tenorangesax/SaxboardTM/Pictures/IMG_7189.jpeg

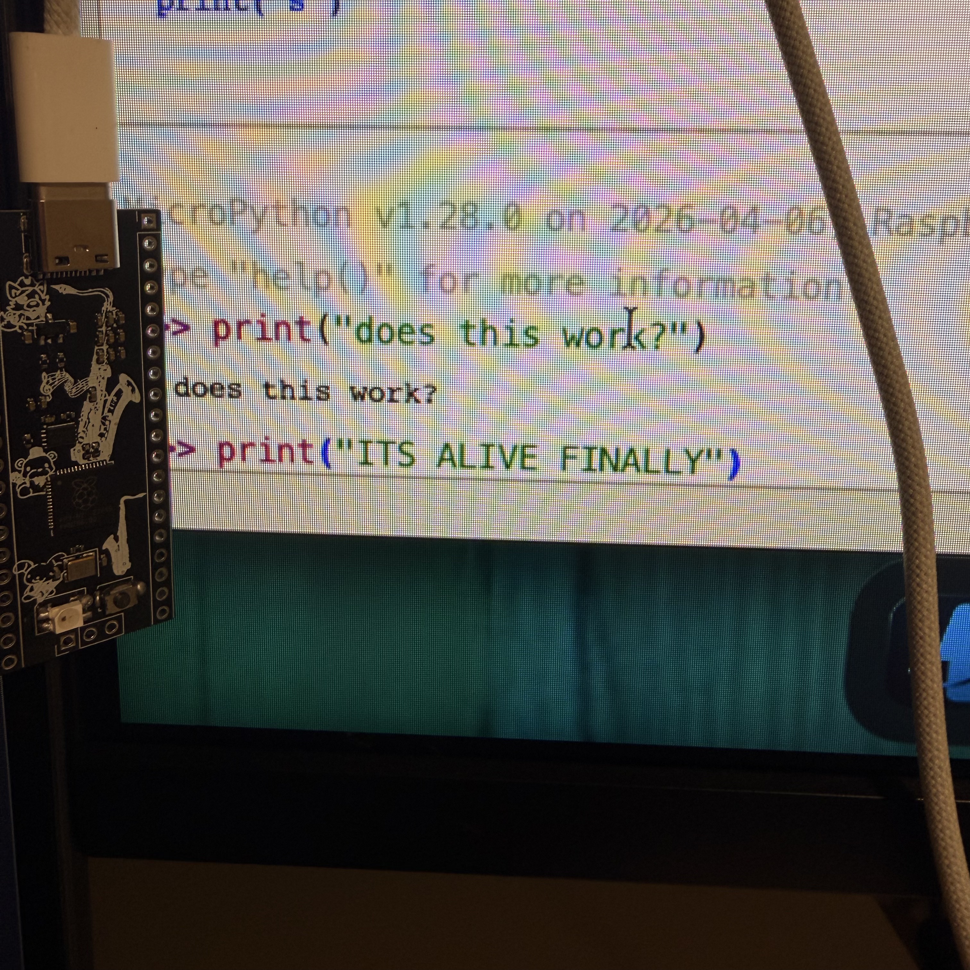
Pictures/IMG_7189.jpeg
