tenorangesax/SaxboardTM/Pictures/IMG_7191.jpeg

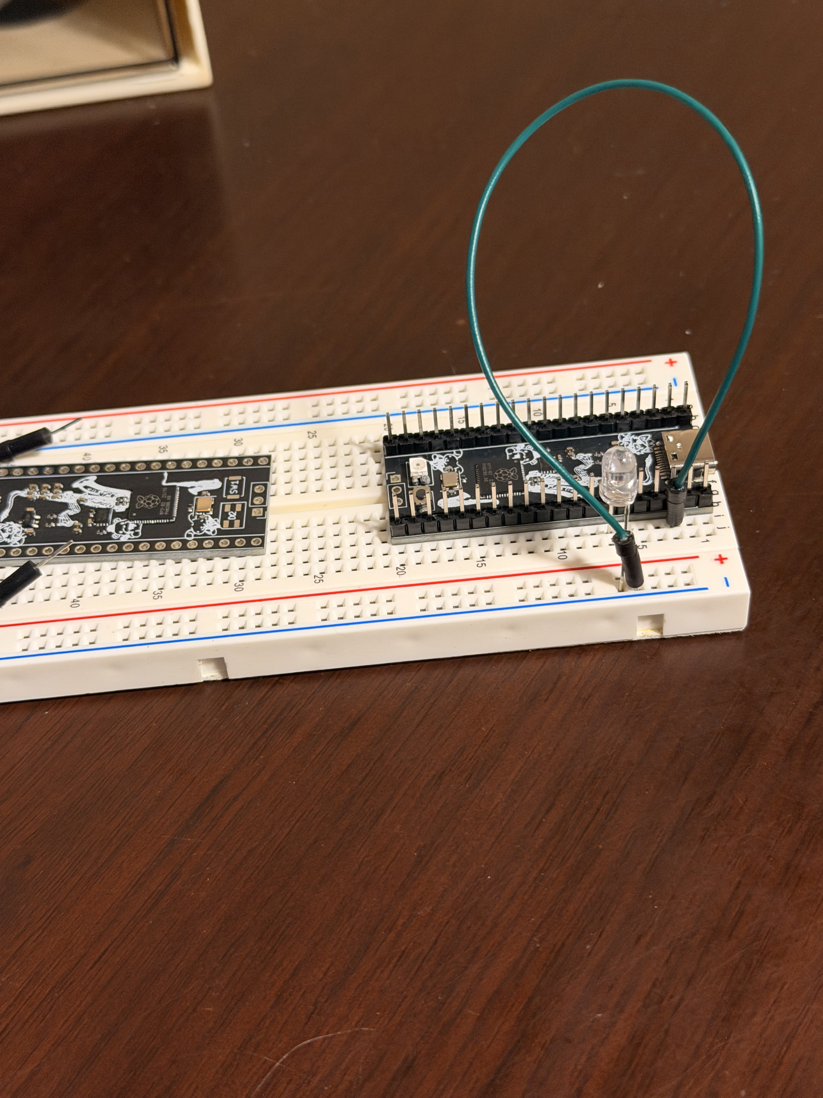
Pictures/IMG_7191.jpeg
