tenorangesax/SaxboardTM/Pictures/1.png

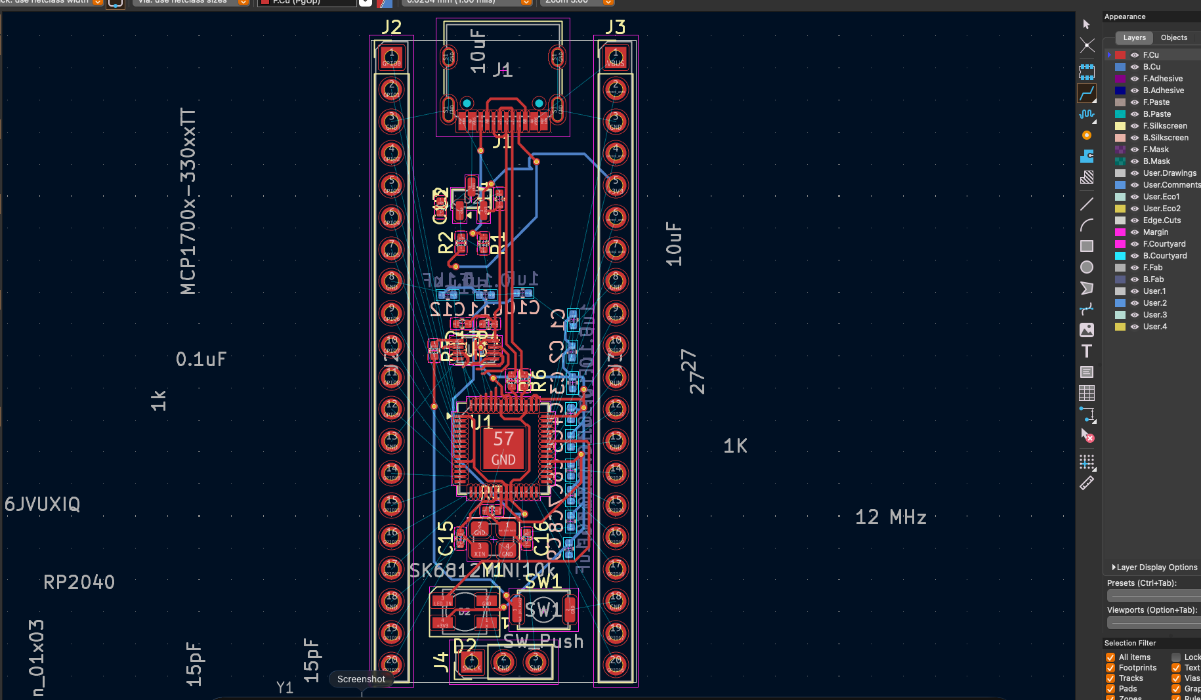
Pictures/1.png
