tenorangesax/SaxboardTM/Pictures/2.png

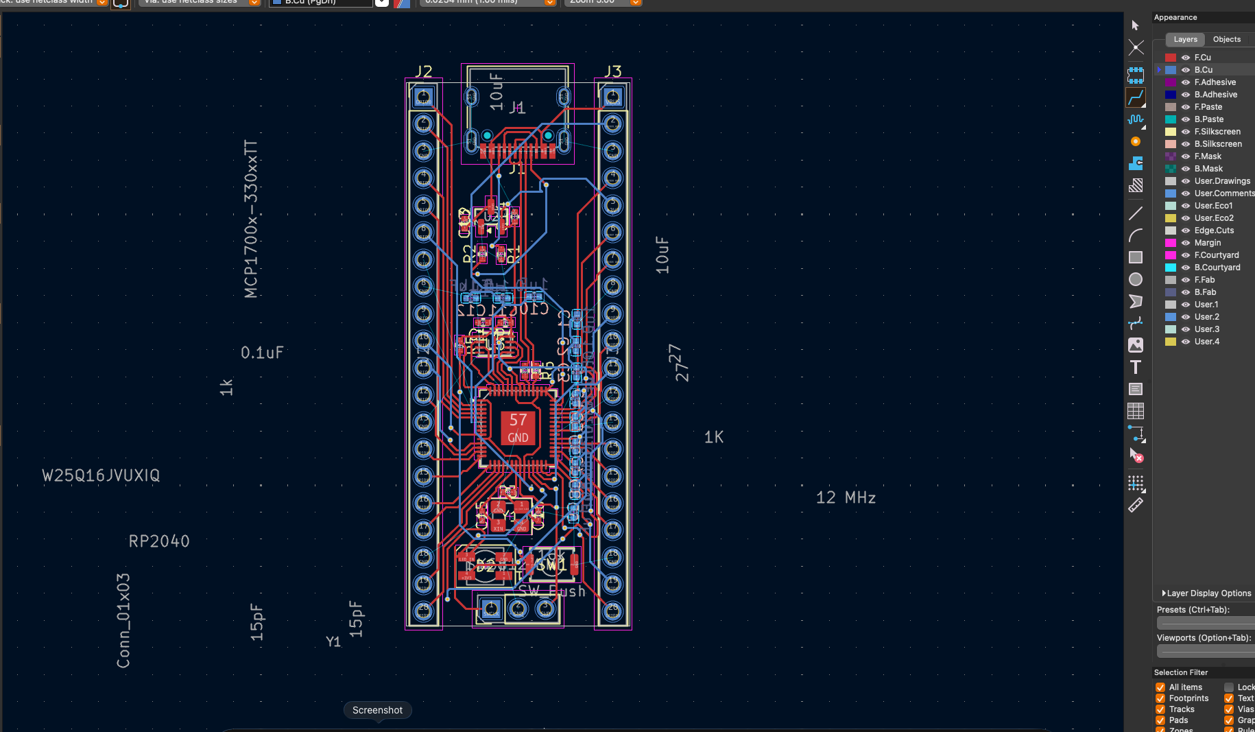
Pictures/2.png
