tenorangesax/SaxboardTM/Pictures/3.png

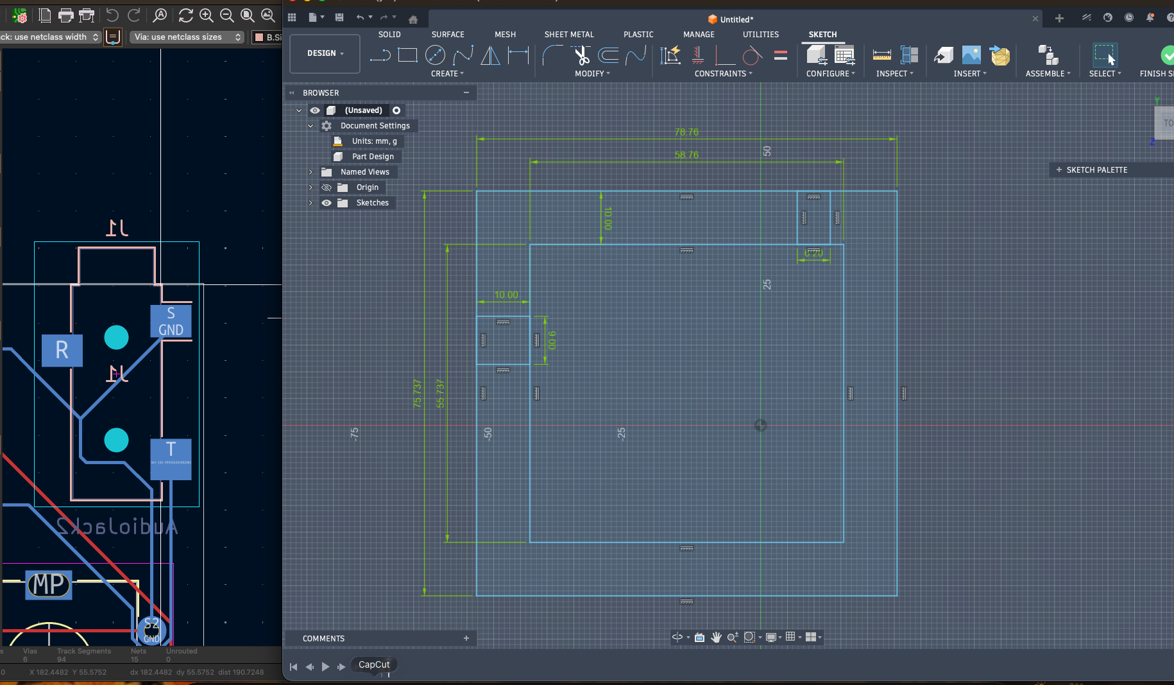
Pictures/3.png
