tenorangesax/SaxboardTM/Pictures/4.png

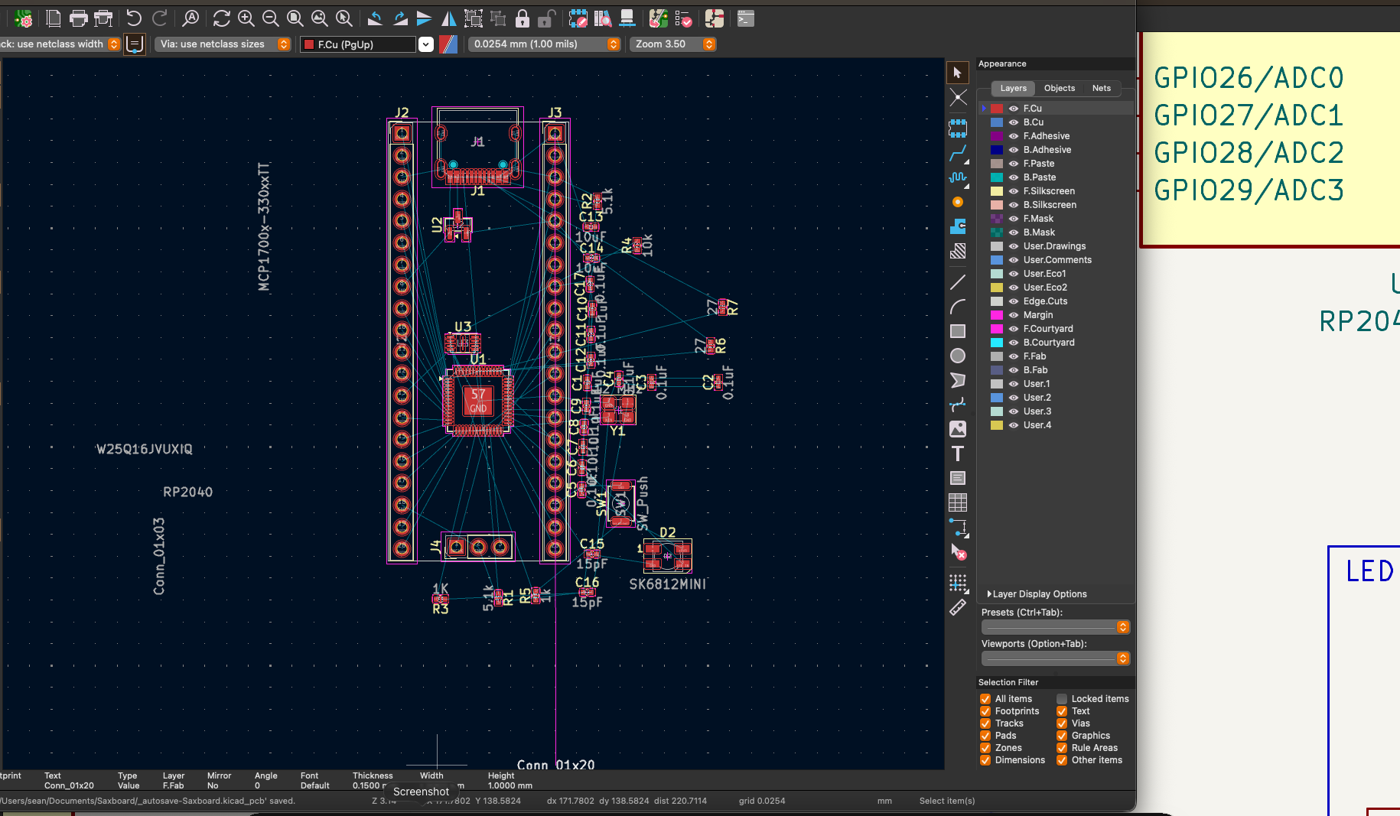
Pictures/4.png
