tenorangesax/SaxboardTM/Pictures/5.png

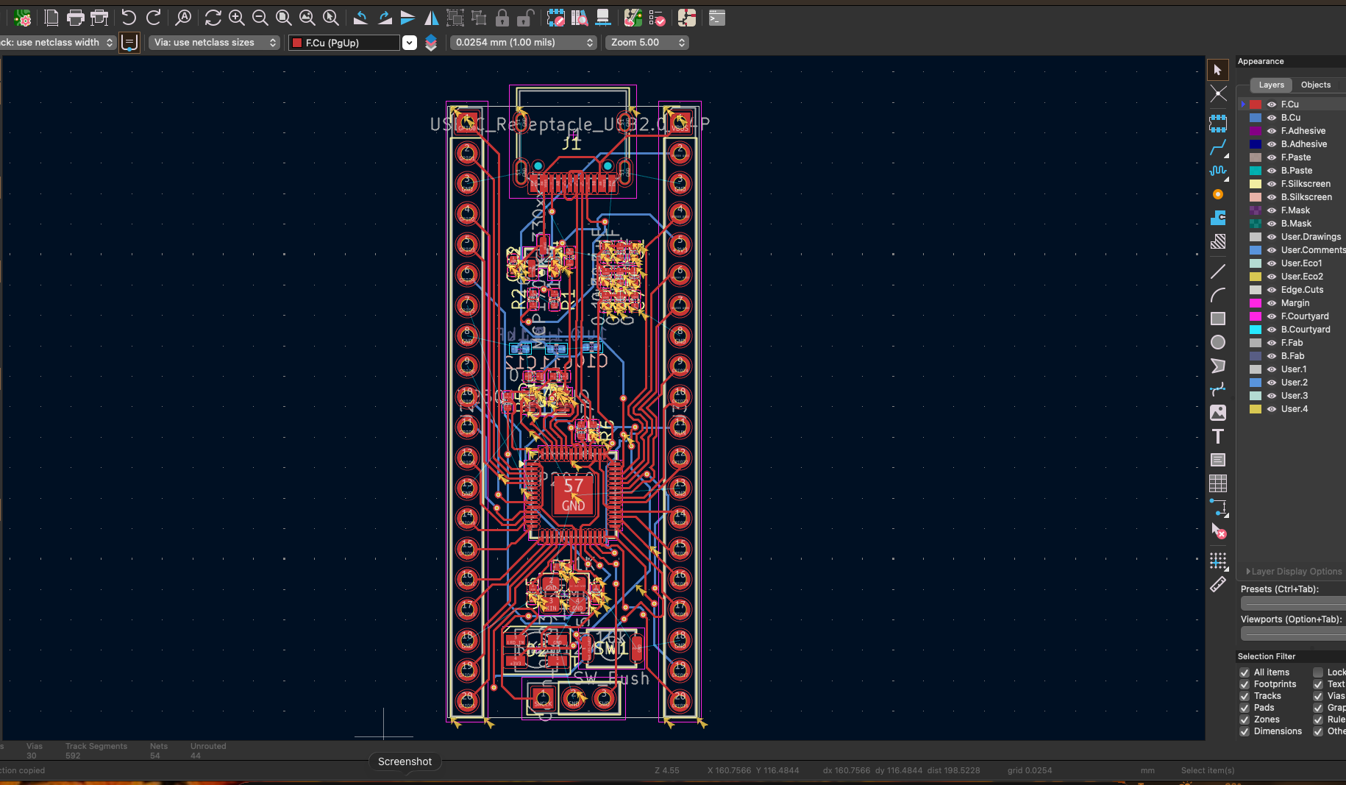
Pictures/5.png
