tenorangesax/SaxboardTM/Pictures/6.png

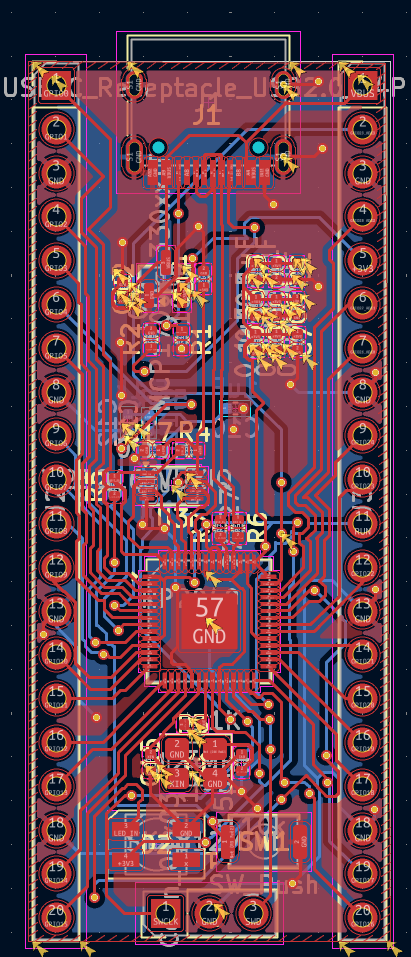
Pictures/6.png
