tenorangesax/SaxboardTM/Pictures/final editor 2.png

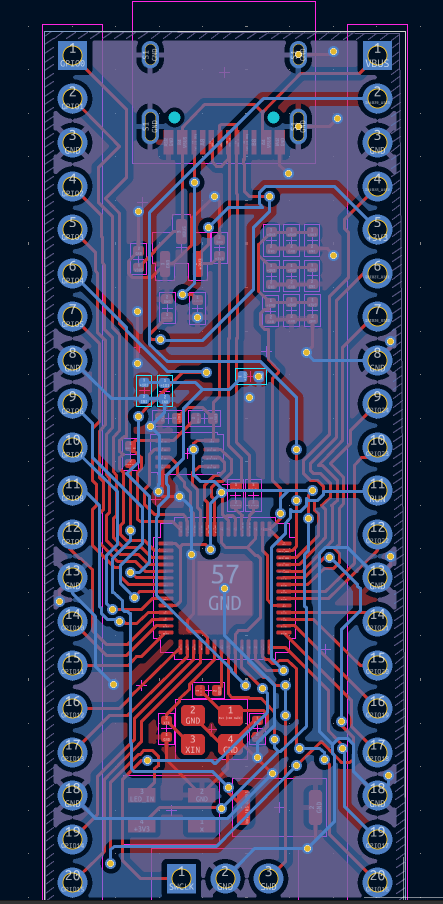
Pictures/final editor 2.png
