tenorangesax/SaxboardTM/Pictures/final editor 3.png

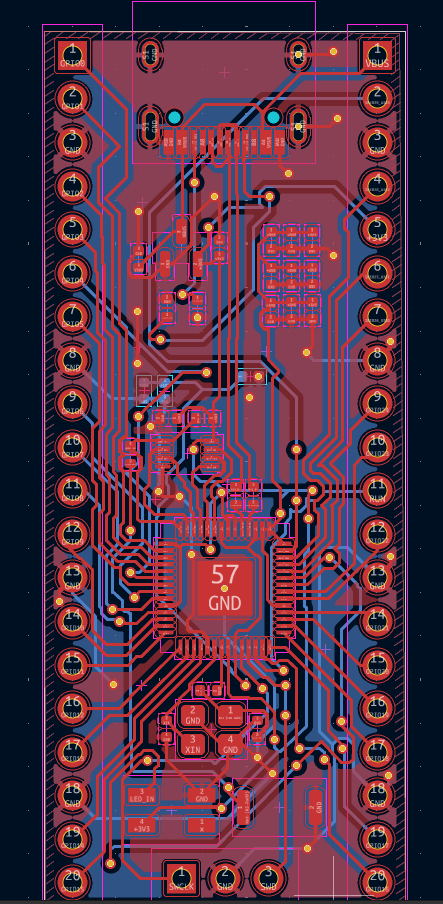
Pictures/final editor 3.png
