tenorangesax/SaxboardTM/Pictures/final editor.png

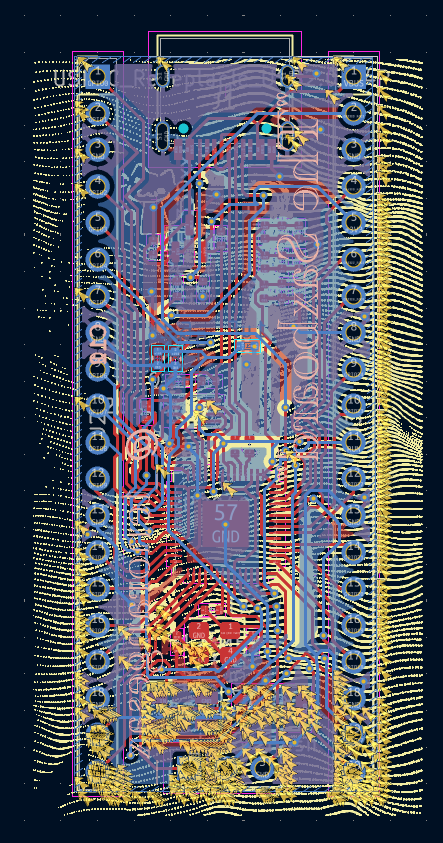
Pictures/final editor.png
