tenorangesax/SaxboardTM/Pictures/Final pcb angle view.png

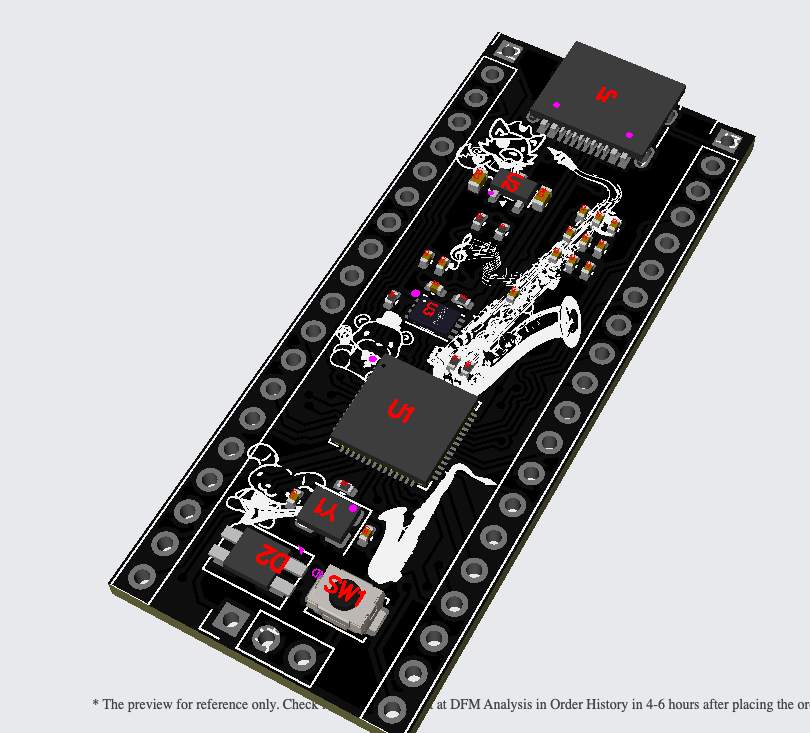
Pictures/Final pcb angle view.png
