tenorangesax/SaxboardTM/Pictures/Final pcb back view.png

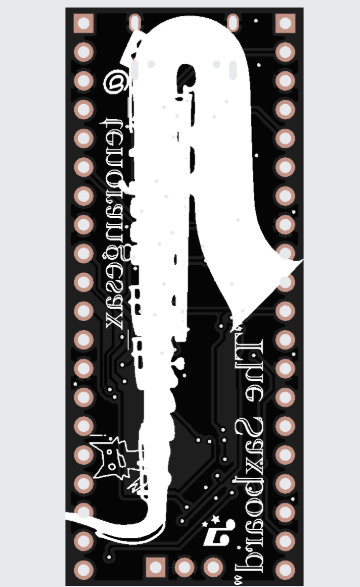
Pictures/Final pcb back view.png
