tenorangesax/SaxboardTM/Pictures/Final pcb front view.png

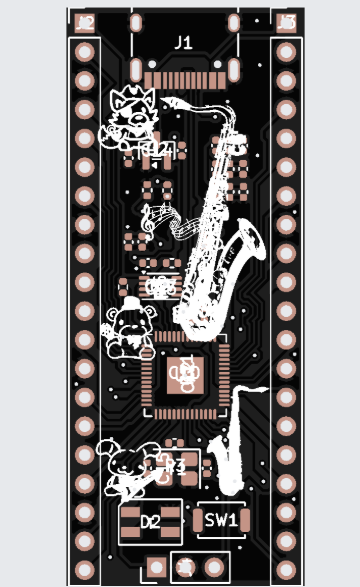
Pictures/Final pcb front view.png
