tenorangesax/SaxboardTM/Pictures/Footprints.png

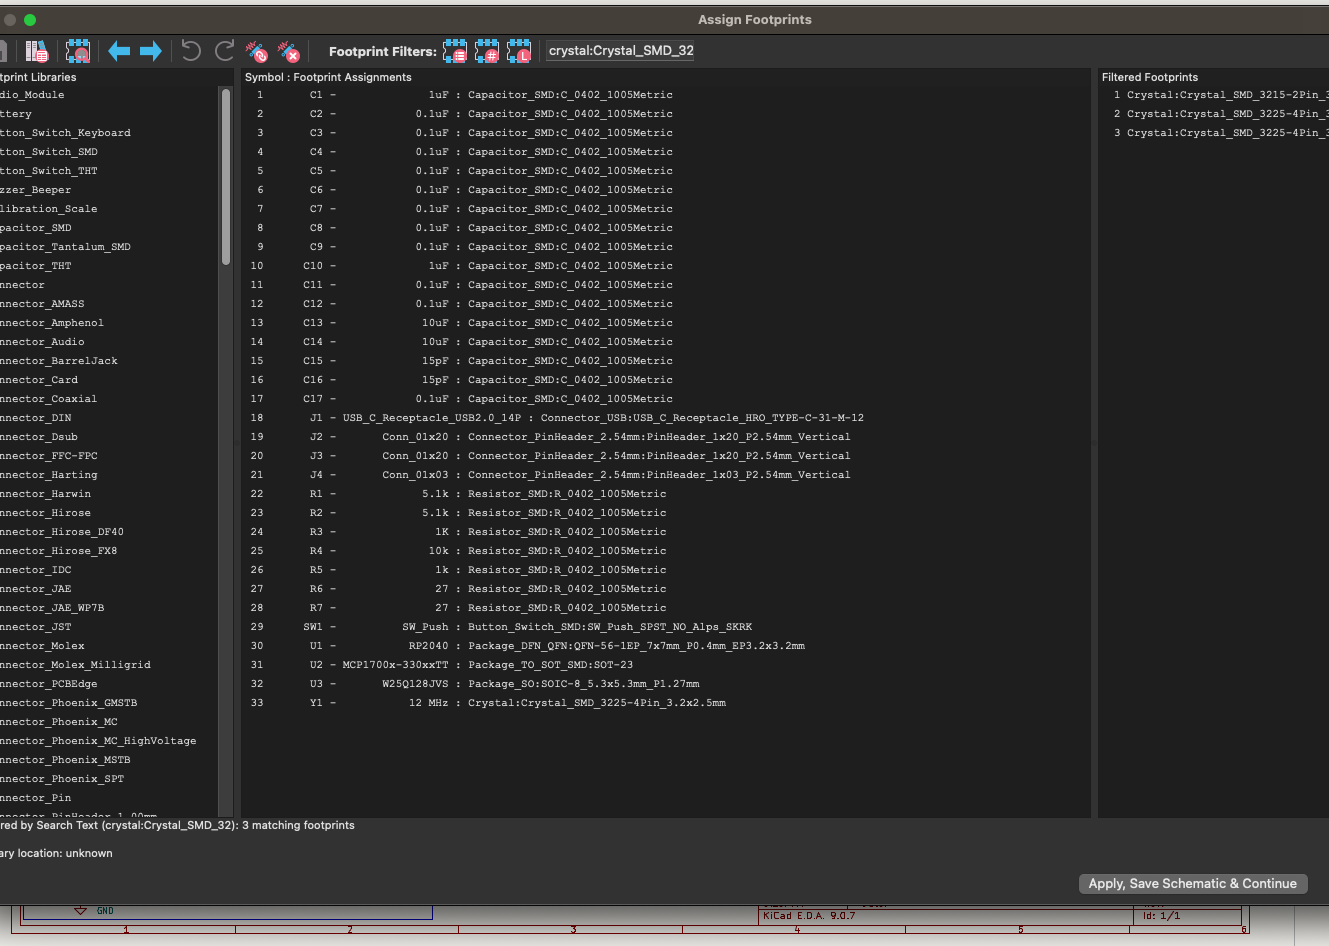
Pictures/Footprints.png
