tenorangesax/SaxboardTM/Pictures/IMG_7158.jpeg

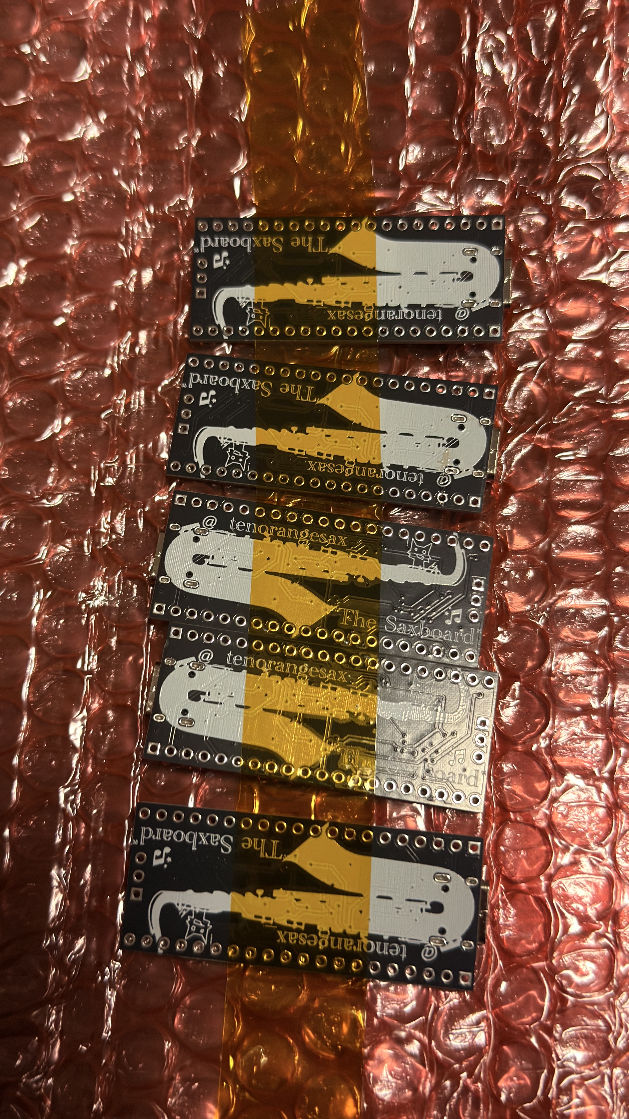
Pictures/IMG_7158.jpeg
