tenorangesax/SaxboardTM/Pictures/IMG_7160.jpeg

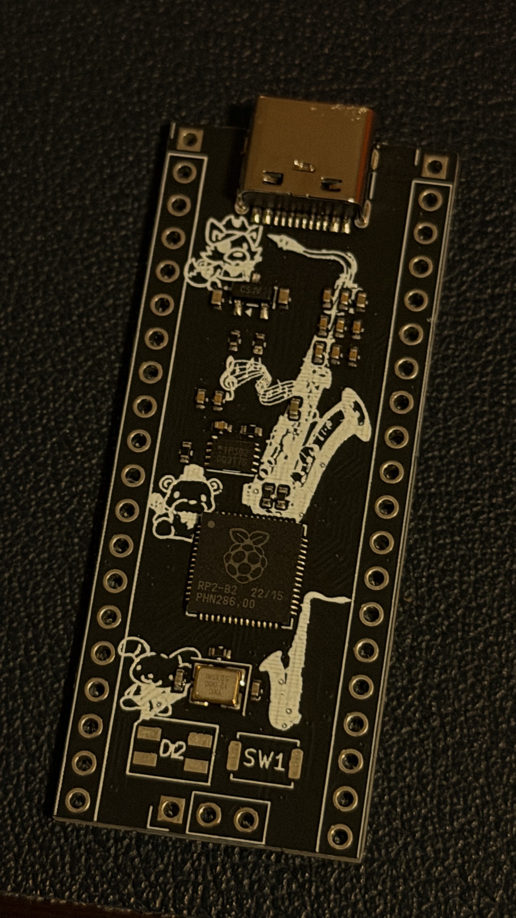
Pictures/IMG_7160.jpeg
