tenorangesax/SaxboardTM/Pictures/IMG_7161.jpeg

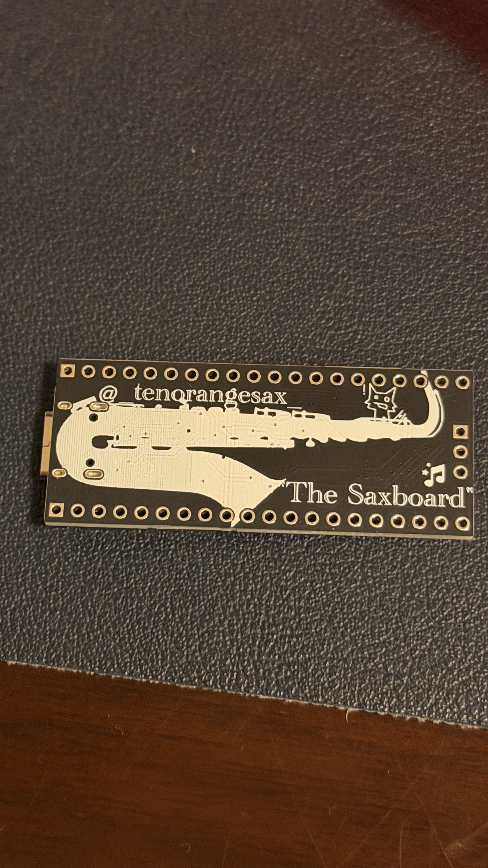
Pictures/IMG_7161.jpeg
