tenorangesax/SaxboardTM/Pictures/IMG_7163.jpeg

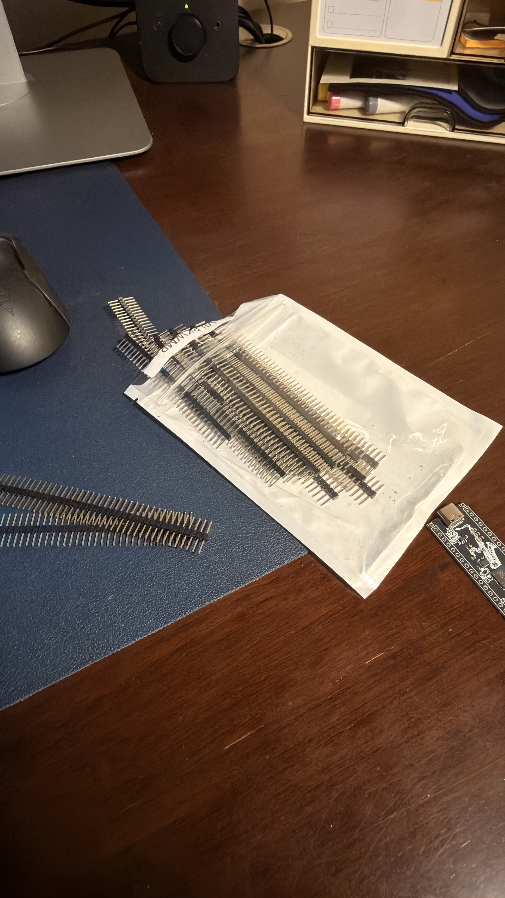
Pictures/IMG_7163.jpeg
