tenorangesax/SaxboardTM/Pictures/IMG_7164.jpeg

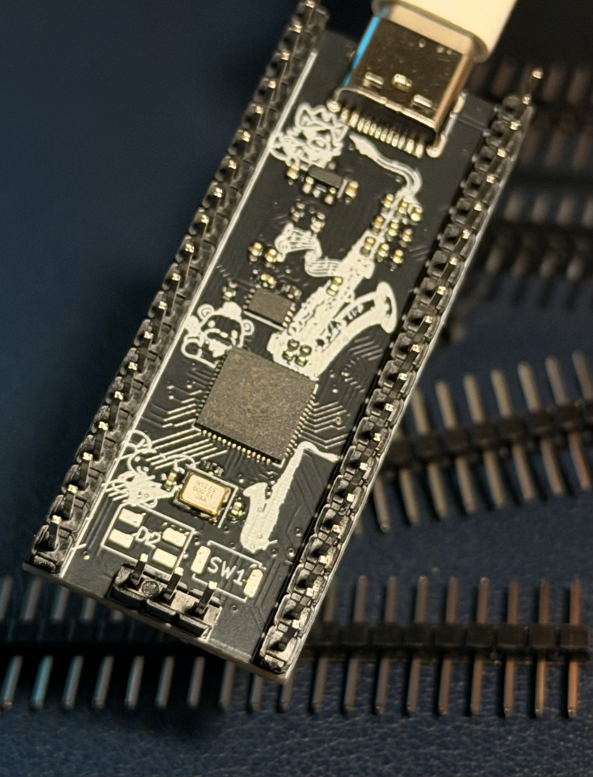
Pictures/IMG_7164.jpeg
