tenorangesax/SaxboardTM/Pictures/IMG_7166.jpeg

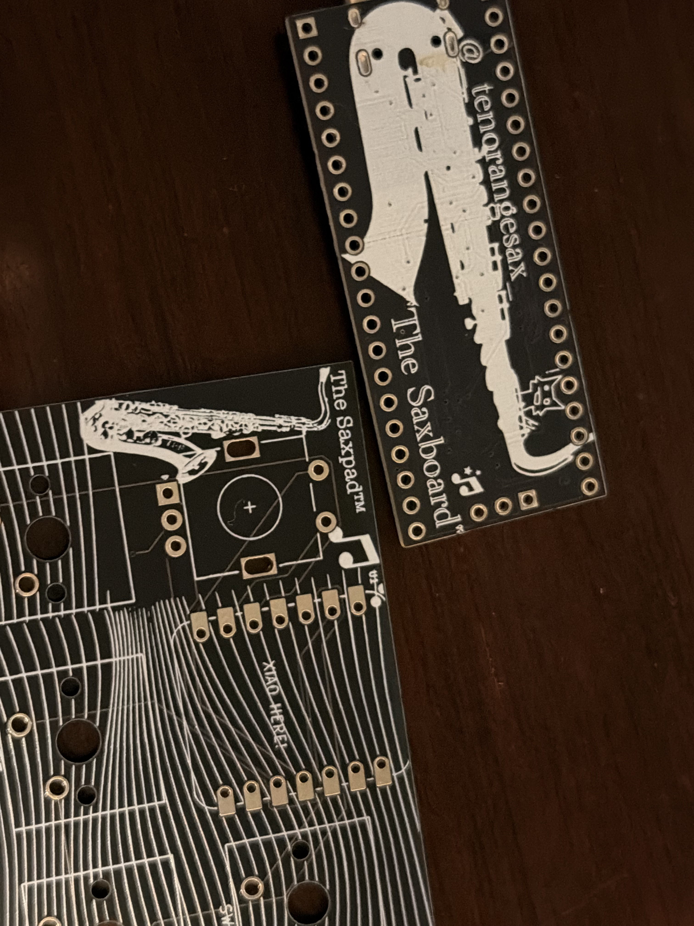
Pictures/IMG_7166.jpeg
