tenorangesax/SaxboardTM/Pictures/IMG_7169.jpeg

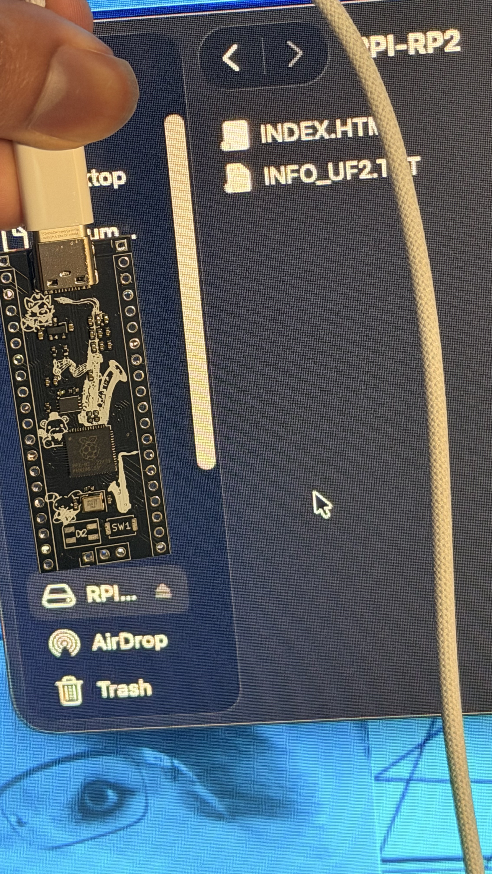
Pictures/IMG_7169.jpeg
