tenorangesax/SaxboardTM/Pictures/IMG_7171.jpeg

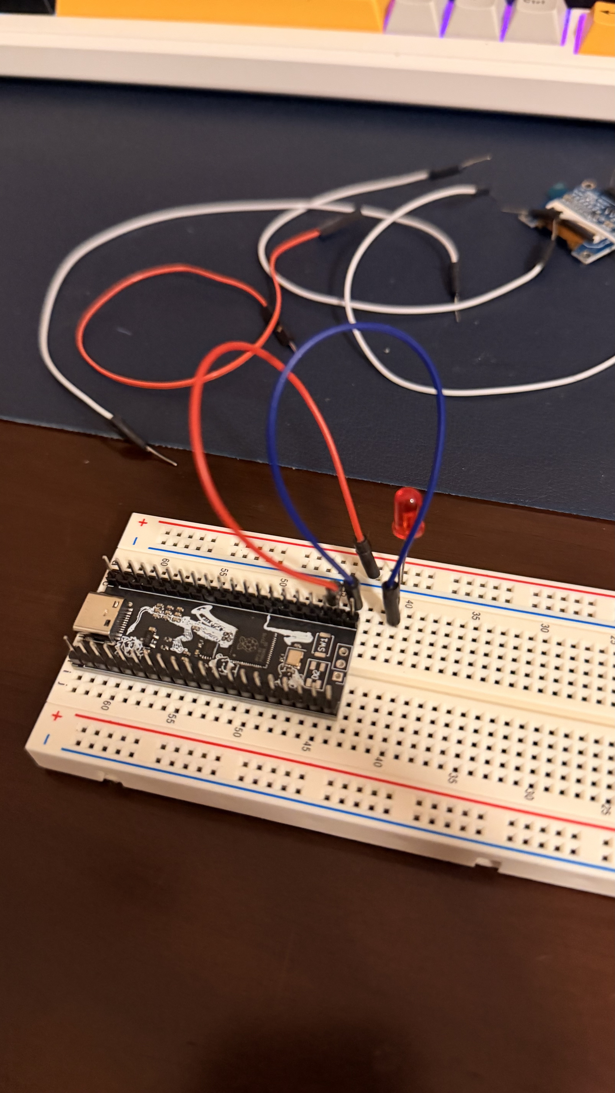
Pictures/IMG_7171.jpeg
