tenorangesax/SaxboardTM/Pictures/Saxboard.png

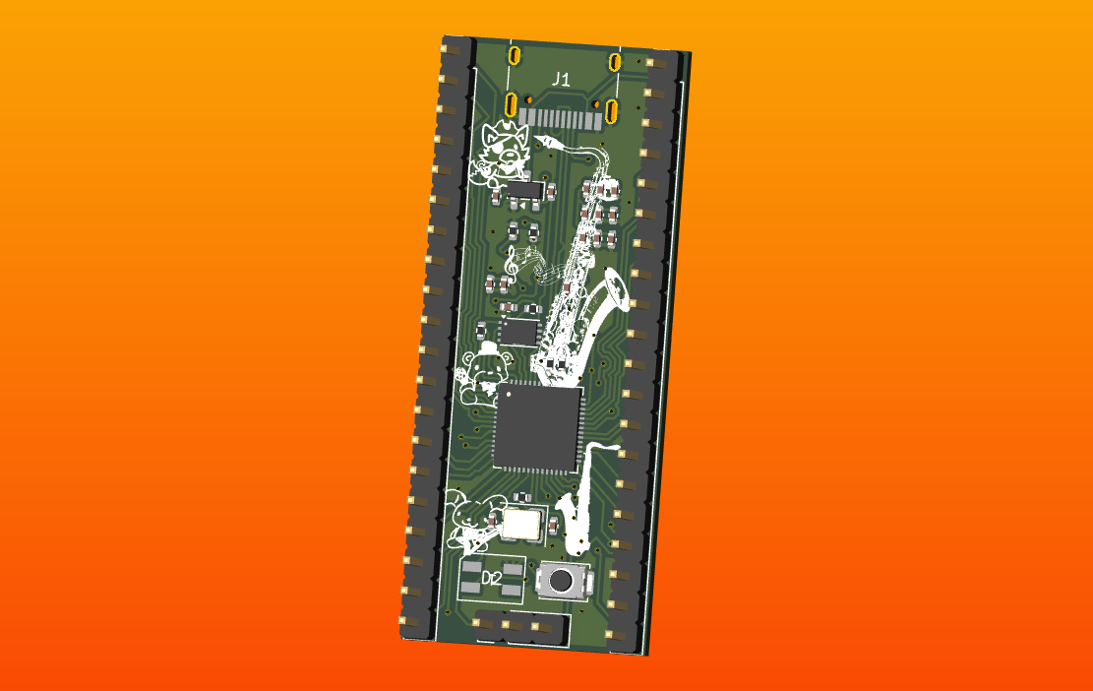
Pictures/Saxboard.png
