tenorangesax/SaxboardTM/Pictures/Saxboard_BACK.png

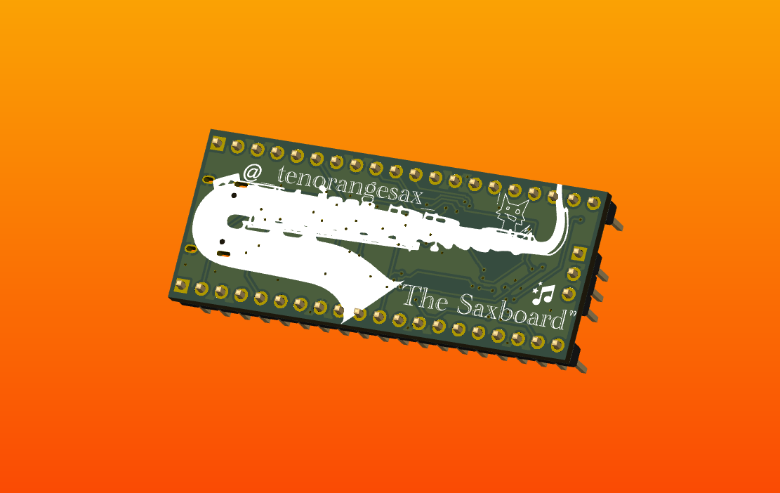
Pictures/Saxboard_BACK.png
